slacky1965/electricity_meter_zrd/doc/images/board/board_3d_box_common.jpg

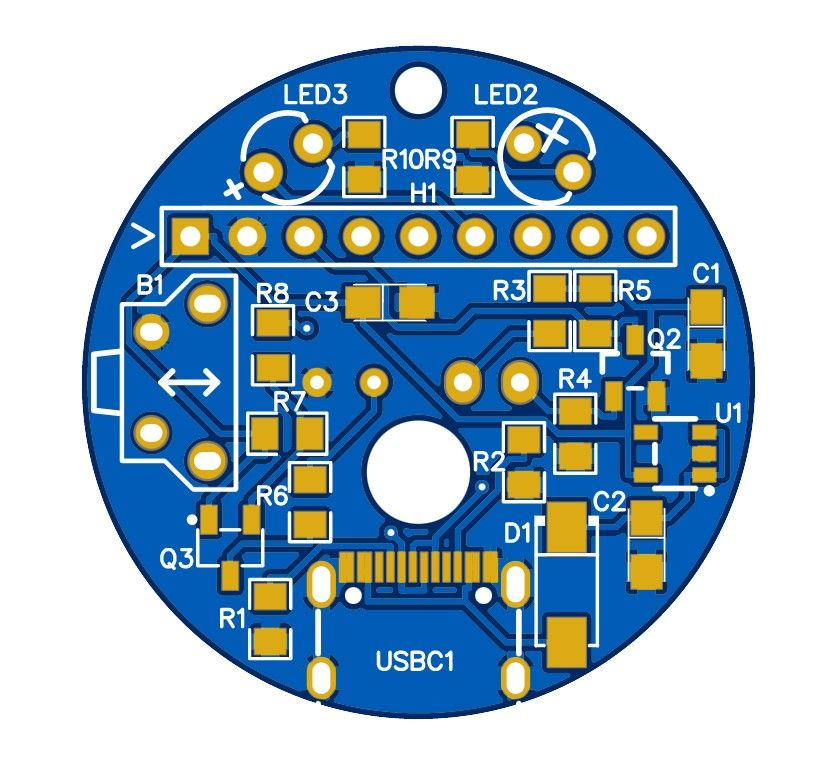
doc/images/board/board_3d_box_common.jpg
