slacky1965/electricity_meter_zrd/doc/images/board/board_ebyte_bottom.png

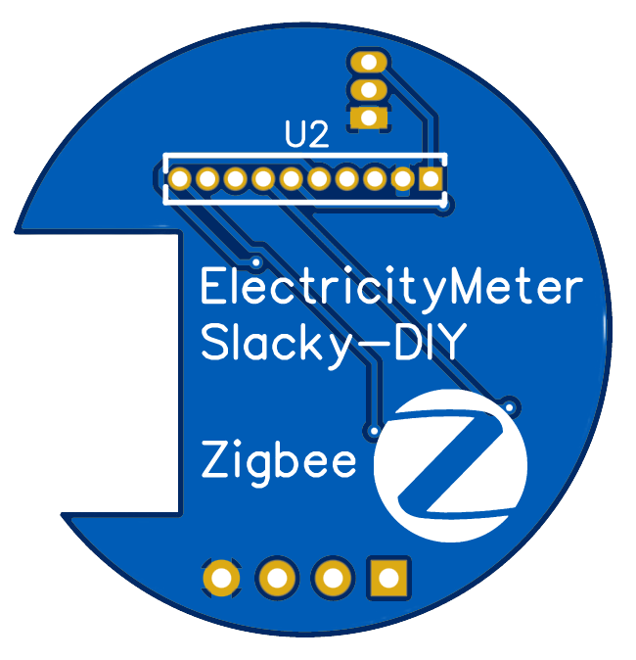
doc/images/board/board_ebyte_bottom.png
