slacky1965/electricity_meter_zrd/doc/images/box/box_common_e180.jpg

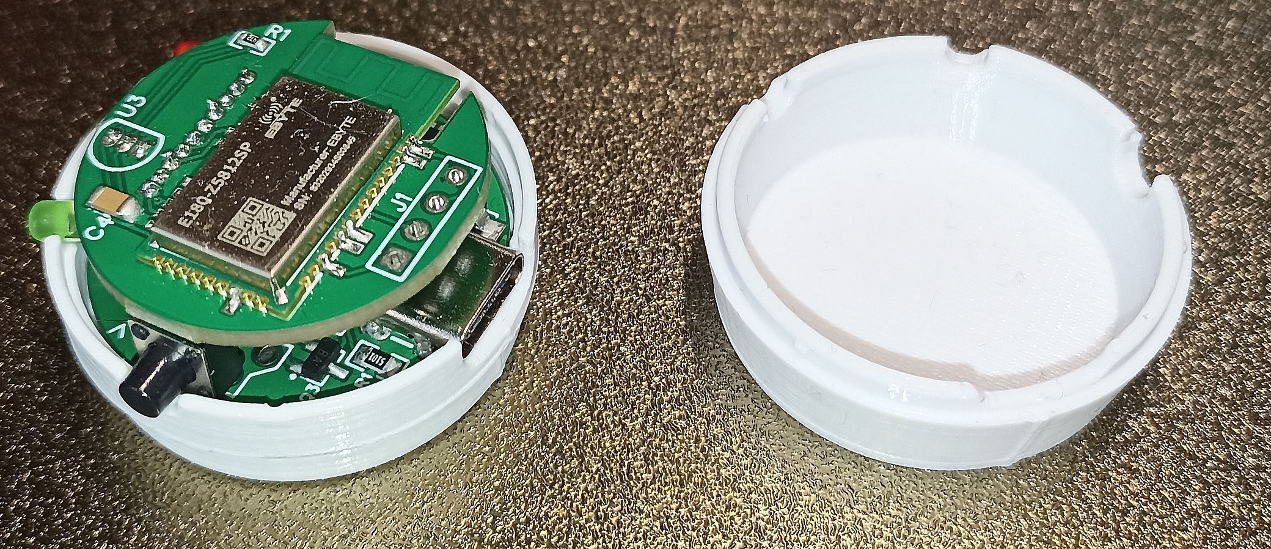
doc/images/box/box_common_e180.jpg
