slacky1965/electricity_meter_zrd/doc/images/box_drawing.jpg

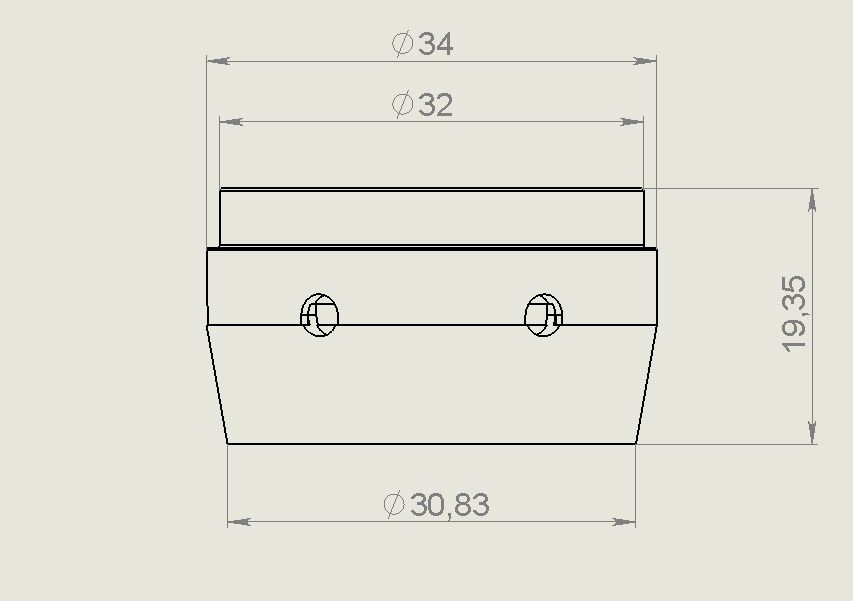
doc/images/box_drawing.jpg
