slacky1965/electricity_meter_zrd/doc/images/device_3d_box1.jpg

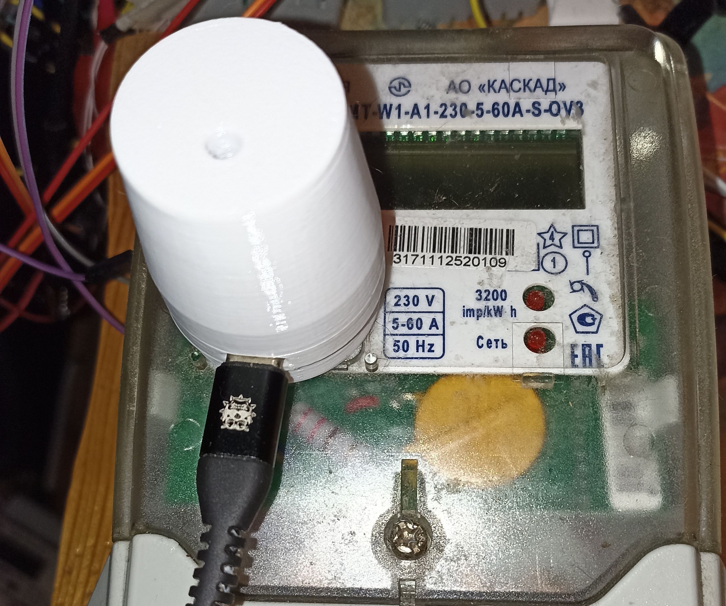
doc/images/device_3d_box1.jpg
