slacky1965/electricity_meter_zrd/doc/images/device_ztu_2.jpg

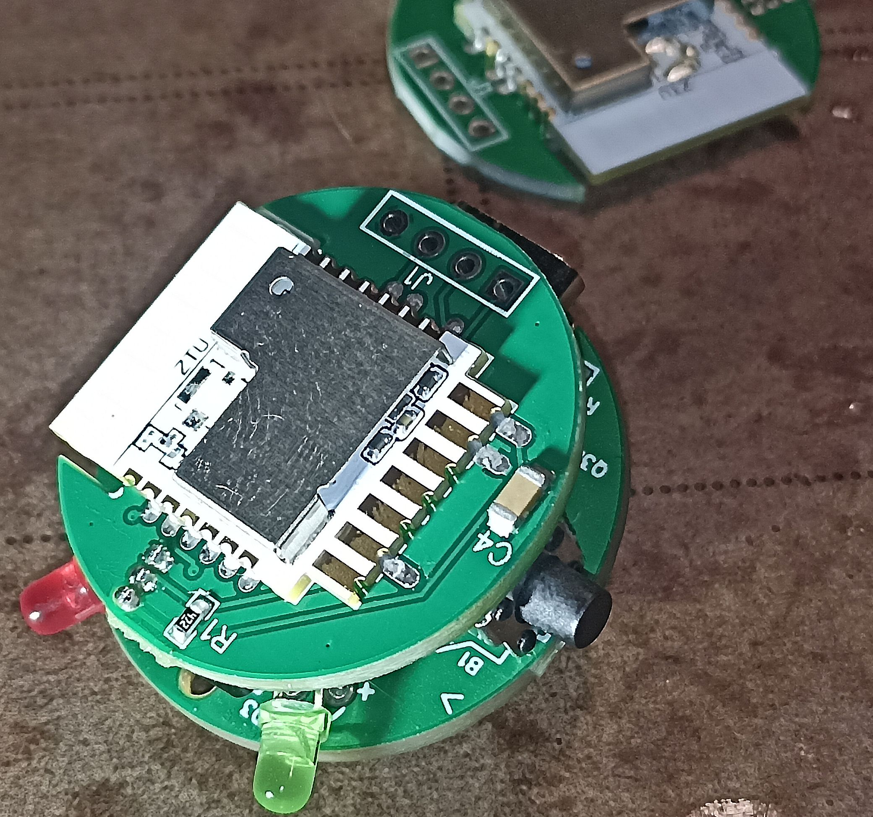
doc/images/device_ztu_2.jpg
