slacky1965/electricity_meter_zrd/doc/images/eclipse/eclipse5.jpg

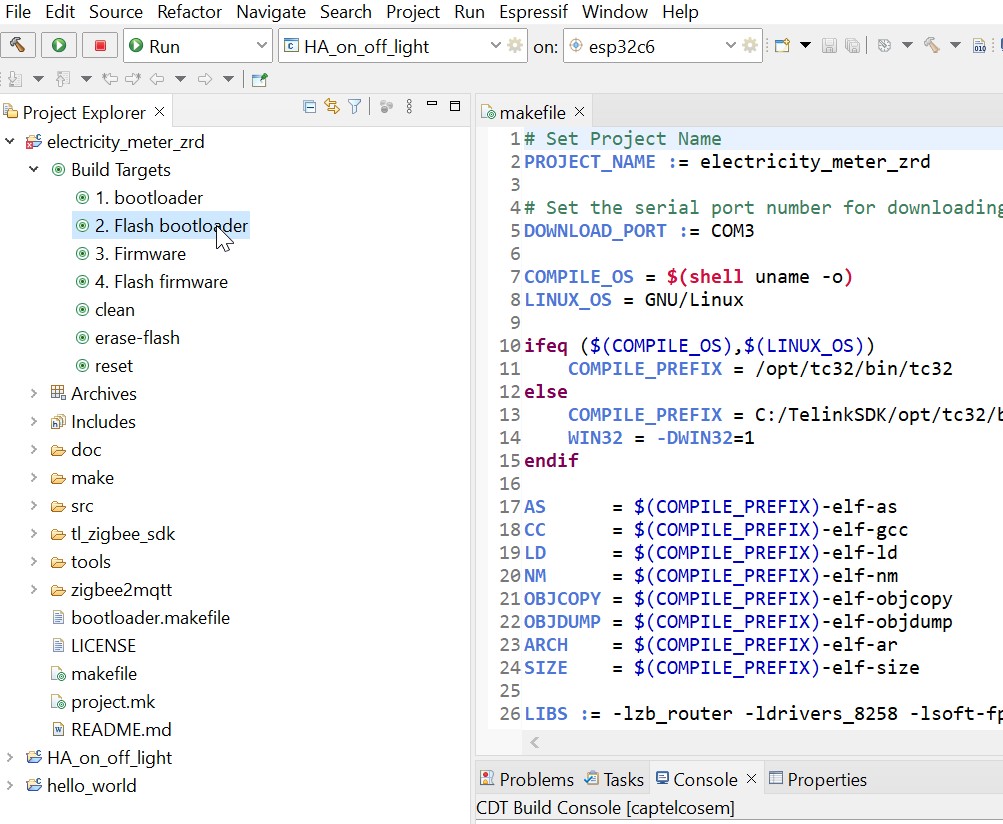
doc/images/eclipse/eclipse5.jpg
