slacky1965/electricity_meter_zrd/src/app_endpoint_cfg.c

#include "app_main.h"

#ifndef ZCL_BASIC_MFG_NAME
#define ZCL_BASIC_MFG_NAME     		{6,'T','E','L','I','N','K'}
#endif
#ifndef ZCL_BASIC_MODEL_ID
#define ZCL_BASIC_MODEL_ID	   		{8,'T','L','S','R','8','2','x','x'}
#endif
#ifndef ZCL_BASIC_SW_BUILD_ID
#define ZCL_BASIC_SW_BUILD_ID     	{10,'0','1','2','2','0','5','2','0','1','7'}
#endif

#define R               ACCESS_CONTROL_READ
#define RW              ACCESS_CONTROL_READ | ACCESS_CONTROL_WRITE
#define RR              ACCESS_CONTROL_READ | ACCESS_CONTROL_REPORTABLE

#define ZCL_UINT8       ZCL_DATA_TYPE_UINT8
#define ZCL_UINT16      ZCL_DATA_TYPE_UINT16
#define ZCL_UINT24      ZCL_DATA_TYPE_UINT24
#define ZCL_UINT32      ZCL_DATA_TYPE_UINT32
#define ZCL_UINT48      ZCL_DATA_TYPE_UINT48
#define ZCL_INT16       ZCL_DATA_TYPE_INT16
#define ZCL_ENUM8       ZCL_DATA_TYPE_ENUM8
#define ZCL_ENUM16      ZCL_DATA_TYPE_ENUM16
#define ZCL_BITMAP8     ZCL_DATA_TYPE_BITMAP8
#define ZCL_BITMAP16    ZCL_DATA_TYPE_BITMAP16
#define ZCL_BITMAP32    ZCL_DATA_TYPE_BITMAP32
#define ZCL_BOOLEAN     ZCL_DATA_TYPE_BOOLEAN
#define ZCL_CHAR_STR    ZCL_DATA_TYPE_CHAR_STR
#define ZCL_OCTET_STR   ZCL_DATA_TYPE_OCTET_STR
#define ZCL_UTC         ZCL_DATA_TYPE_UTC
#define ZCL_IEEE_ADDR   ZCL_DATA_TYPE_IEEE_ADDR

/**
 *  @brief Definition for Incoming cluster / Sever Cluster
 */
const uint16_t app_inClusterList[] = {
    ZCL_CLUSTER_GEN_BASIC,
    ZCL_CLUSTER_GEN_IDENTIFY,
#ifdef ZCL_ZLL_COMMISSIONING
    ZCL_CLUSTER_TOUCHLINK_COMMISSIONING,
#endif
#ifdef ZCL_POLL_CTRL
    ZCL_CLUSTER_GEN_POLL_CONTROL,
#endif
    ZCL_CLUSTER_SE_METERING,
    ZCL_CLUSTER_MS_ELECTRICAL_MEASUREMENT,
    ZCL_CLUSTER_GEN_DEVICE_TEMP_CONFIG,
};

/**
 *  @brief Definition for Outgoing cluster / Client Cluster
 */
const uint16_t app_outClusterList[] = {
    ZCL_CLUSTER_GEN_BASIC,
#ifdef ZCL_GROUP
    ZCL_CLUSTER_GEN_GROUPS,
#endif
#ifdef ZCL_SCENE
    ZCL_CLUSTER_GEN_SCENES,
#endif
#ifdef ZCL_ON_OFF
    ZCL_CLUSTER_GEN_ON_OFF,
#endif
#ifdef ZCL_LEVEL_CTRL
    ZCL_CLUSTER_GEN_LEVEL_CONTROL,
#endif
#ifdef ZCL_OTA
    ZCL_CLUSTER_OTA,
#endif
#ifdef ZCL_ZLL_COMMISSIONING
    ZCL_CLUSTER_TOUCHLINK_COMMISSIONING,
#endif
    ZCL_CLUSTER_GEN_TIME,
    ZCL_CLUSTER_SE_METERING,
};

/**
 *  @brief Definition for Server cluster number and Client cluster number
 */
#define APP_IN_CLUSTER_NUM      (sizeof(app_inClusterList)/sizeof(app_inClusterList[0]))
#define APP_OUT_CLUSTER_NUM     (sizeof(app_outClusterList)/sizeof(app_outClusterList[0]))

/**
 *  @brief Definition for simple description for HA profile
 */
const af_simple_descriptor_t app_simpleDesc =
{
    HA_PROFILE_ID,                          /* Application profile identifier */
    HA_DEV_METER_INTERFACE,                 /* Application device identifier */
    APP_ENDPOINT_1,                         /* Endpoint */
    1,                                      /* Application device version */
    0,                                      /* Reserved */
    APP_IN_CLUSTER_NUM,                     /* Application input cluster count */
    APP_OUT_CLUSTER_NUM,                    /* Application output cluster count */
    (uint16_t *)app_inClusterList,          /* Application input cluster list */
    (uint16_t *)app_outClusterList,         /* Application output cluster list */
};

/* Basic */
zcl_basicAttr_t g_zcl_basicAttrs =
{
    .zclVersion     = 0x03,
    .appVersion     = APP_RELEASE,
    .stackVersion   = (STACK_RELEASE|STACK_BUILD),
    .hwVersion      = HW_VERSION,
    .manuName       = ZCL_BASIC_MFG_NAME,
    .modelId        = ZCL_BASIC_MODEL_ID,
    .dateCode       = ZCL_BASIC_DATE_CODE,
    .powerSource    = POWER_SOURCE_MAINS_1_PHASE,
    .swBuildId      = ZCL_BASIC_SW_BUILD_ID,
    .deviceEnable   = TRUE,
};

uint8_t zclVersionServer;

const zclAttrInfo_t basic_attrTbl[] =
{
    { ZCL_ATTRID_BASIC_ZCL_VER,             ZCL_UINT8,      R,  (uint8_t*)&g_zcl_basicAttrs.zclVersion      },
    { ZCL_ATTRID_BASIC_APP_VER,             ZCL_UINT8,      R,  (uint8_t*)&g_zcl_basicAttrs.appVersion      },
    { ZCL_ATTRID_BASIC_STACK_VER,           ZCL_UINT8,      R,  (uint8_t*)&g_zcl_basicAttrs.stackVersion    },
    { ZCL_ATTRID_BASIC_HW_VER,              ZCL_UINT8,      R,  (uint8_t*)&g_zcl_basicAttrs.hwVersion       },
    { ZCL_ATTRID_BASIC_MFR_NAME,            ZCL_CHAR_STR,   R,  (uint8_t*)g_zcl_basicAttrs.manuName         },
    { ZCL_ATTRID_BASIC_MODEL_ID,            ZCL_CHAR_STR,   R,  (uint8_t*)g_zcl_basicAttrs.modelId          },
    { ZCL_ATTRID_BASIC_DATE_CODE,           ZCL_CHAR_STR,   R,  (uint8_t*)g_zcl_basicAttrs.dateCode         },
    { ZCL_ATTRID_BASIC_POWER_SOURCE,        ZCL_ENUM8,      R,  (uint8_t*)&g_zcl_basicAttrs.powerSource     },
    { ZCL_ATTRID_BASIC_DEV_ENABLED,         ZCL_BOOLEAN,    RW, (uint8_t*)&g_zcl_basicAttrs.deviceEnable    },
    { ZCL_ATTRID_BASIC_SW_BUILD_ID,         ZCL_CHAR_STR,   R,  (uint8_t*)&g_zcl_basicAttrs.swBuildId       },

    { ZCL_ATTRID_GLOBAL_CLUSTER_REVISION,   ZCL_UINT16,     R,  (uint8_t*)&zcl_attr_global_clusterRevision  },
};

#define ZCL_BASIC_ATTR_NUM    sizeof(basic_attrTbl) / sizeof(zclAttrInfo_t)

uint8_t zclVersionServer;

const zclAttrInfo_t version_attrTbl[] =
{
    { ZCL_ATTRID_BASIC_ZCL_VER,             ZCL_UINT8,      R,  (uint8_t*)&zclVersionServer                 },

    { ZCL_ATTRID_GLOBAL_CLUSTER_REVISION,   ZCL_UINT16,     R,  (uint8_t*)&zcl_attr_global_clusterRevision  },
};

#define ZCL_BASIC_SERVER_ATTR_NUM    sizeof(version_attrTbl) / sizeof(zclAttrInfo_t)


/* Identify */
zcl_identifyAttr_t g_zcl_identifyAttrs =
{
    .identifyTime   = 0x0000,
};

const zclAttrInfo_t identify_attrTbl[] =
{
    { ZCL_ATTRID_IDENTIFY_TIME,             ZCL_UINT16,     RW, (uint8_t*)&g_zcl_identifyAttrs.identifyTime },

    { ZCL_ATTRID_GLOBAL_CLUSTER_REVISION,   ZCL_UINT16,     R,  (uint8_t*)&zcl_attr_global_clusterRevision  },
};

#define ZCL_IDENTIFY_ATTR_NUM    sizeof(identify_attrTbl) / sizeof(zclAttrInfo_t)

zcl_timeAttr_t g_zcl_timeAttrs = {
    .time_utc = 0xffffffff,
};

const zclAttrInfo_t time_attrTbl[] =
{
    { ZCL_ATTRID_TIME,                      ZCL_UTC,    RW, (uint8_t*)&g_zcl_timeAttrs.time_utc         },

    { ZCL_ATTRID_GLOBAL_CLUSTER_REVISION,   ZCL_UINT16, R,  (uint8_t*)&zcl_attr_global_clusterRevision  },
};

#define ZCL_TIME_ATTR_NUM    sizeof(time_attrTbl) / sizeof(zclAttrInfo_t)

zcl_seAttr_t g_zcl_seAttrs = {
    .tariff_1 = 0,
    .tariff_2 = 0,
    .tariff_3 = 0,
    .tariff_4 = 0,
    .unit_of_measure = 0x00,                                        // kWh
    .multiplier = 1,
    .divisor = 1,
    .summation_formatting = 0xFA,                                   // bit7 - 1, bit6-bit3 - 15, bit2-bit0 - 2 (b11111010)
    .status = 0,
    .device_type = 0,                                               // 0 - Electric Metering
    .battery_percentage = 100,
    .serial_number = {8,'1','1','1','1','1','1','1','1'},
    .date_release = {10,'x','x','.','x','x','.','x','x','x','x'},
    .device_model = DEVICE_UNDEFINED, // Electric Metering
    .device_address = 0,
    .device_name = {9,'N','o',' ','D','e','v','i','c','e'},
    .device_password = {1, '0'},
    .measurement_period = DEFAULT_MEASUREMENT_PERIOD,
};

const zclAttrInfo_t se_attrTbl[] = {
    {ZCL_ATTRID_CURRENT_SUMMATION_DELIVERD,         ZCL_UINT48,     RR, (uint8_t*)&g_zcl_seAttrs.cur_sum_delivered      },
    {ZCL_ATTRID_CURRENT_TIER_1_SUMMATION_DELIVERD,  ZCL_UINT48,     RR, (uint8_t*)&g_zcl_seAttrs.tariff_1               },
    {ZCL_ATTRID_CURRENT_TIER_2_SUMMATION_DELIVERD,  ZCL_UINT48,     RR, (uint8_t*)&g_zcl_seAttrs.tariff_2               },
    {ZCL_ATTRID_CURRENT_TIER_3_SUMMATION_DELIVERD,  ZCL_UINT48,     RR, (uint8_t*)&g_zcl_seAttrs.tariff_3               },
    {ZCL_ATTRID_CURRENT_TIER_4_SUMMATION_DELIVERD,  ZCL_UINT48,     RR, (uint8_t*)&g_zcl_seAttrs.tariff_4               },
    {ZCL_ATTRID_STATUS,                             ZCL_BITMAP8,    RR,  (uint8_t*)&g_zcl_seAttrs.status                },
    {ZCL_ATTRID_UNIT_OF_MEASURE,                    ZCL_UINT8,      R,  (uint8_t*)&g_zcl_seAttrs.unit_of_measure        },
    {ZCL_ATTRID_MULTIPLIER,                         ZCL_UINT24,     RR, (uint8_t*)&g_zcl_seAttrs.multiplier             },
    {ZCL_ATTRID_DIVISOR,                            ZCL_UINT24,     RR, (uint8_t*)&g_zcl_seAttrs.divisor                },
    {ZCL_ATTRID_SUMMATION_FORMATTING,               ZCL_BITMAP8,    R,  (uint8_t*)&g_zcl_seAttrs.summation_formatting   },
    {ZCL_ATTRID_REMAINING_BATTERY_LIFE,             ZCL_UINT8,      RR, (uint8_t*)&g_zcl_seAttrs.battery_percentage     },
    {ZCL_ATTRID_METER_SERIAL_NUMBER,                ZCL_OCTET_STR,  RR, (uint8_t*)&g_zcl_seAttrs.serial_number          },
    {ZCL_ATTRID_METERING_DEVICE_TYPE,               ZCL_BITMAP8,    R,  (uint8_t*)&g_zcl_seAttrs.device_type            },
    {ZCL_ATTRID_CUSTOM_DEVICE_MANUFACTURER,         ZCL_ENUM8,      RW, (uint8_t*)&g_zcl_seAttrs.device_model           },
    {ZCL_ATTRID_CUSTOM_DEVICE_ADDRESS,              ZCL_UINT32,     RW, (uint8_t*)&g_zcl_seAttrs.device_address         },
    {ZCL_ATTRID_CUSTOM_DEVICE_PASSWORD,             ZCL_OCTET_STR,  RW, (uint8_t*)&g_zcl_seAttrs.device_password        },
    {ZCL_ATTRID_CUSTOM_MEASUREMENT_PERIOD,          ZCL_UINT8,      RW, (uint8_t*)&g_zcl_seAttrs.measurement_period     },
    {ZCL_ATTRID_CUSTOM_DATE_RELEASE,                ZCL_OCTET_STR,  RR, (uint8_t*)&g_zcl_seAttrs.date_release           },
    {ZCL_ATTRID_CUSTOM_DEVICE_MODEL,                ZCL_OCTET_STR,  RR, (uint8_t*)&g_zcl_seAttrs.device_name            },

    { ZCL_ATTRID_GLOBAL_CLUSTER_REVISION,           ZCL_UINT16,     R,  (uint8_t*)&zcl_attr_global_clusterRevision      },
};

#define ZCL_SE_ATTR_NUM    sizeof(se_attrTbl) / sizeof(zclAttrInfo_t)

zcl_msAttr_t g_zcl_msAttrs = {
    .type = 0x09,               // bit0: Active measurement (AC). bit3: Phase A measurement
    .current = 0xffff,
    .current_multiplier = 1,
    .current_divisor = 1,
    .voltage = 0xffff,
    .voltage_multiplier = 1,
    .voltage_divisor = 1,
    .power = 0xffff,
    .power_multiplier = 1,
    .power_divisor = 1,
};

const zclAttrInfo_t ms_attrTbl[] = {
    {ZCL_ATTRID_MEASUREMENT_TYPE,           ZCL_BITMAP32, R,    (uint8_t*)&g_zcl_msAttrs.type               },
    {ZCL_ATTRID_LINE_CURRENT,               ZCL_UINT16,   RR,   (uint8_t*)&g_zcl_msAttrs.current            },
    {ZCL_ATTRID_AC_CURRENT_MULTIPLIER,      ZCL_UINT16,   RR,   (uint8_t*)&g_zcl_msAttrs.current_multiplier },
    {ZCL_ATTRID_AC_CURRENT_DIVISOR,         ZCL_UINT16,   RR,   (uint8_t*)&g_zcl_msAttrs.current_divisor    },
    {ZCL_ATTRID_RMS_VOLTAGE,                ZCL_UINT16,   RR,   (uint8_t*)&g_zcl_msAttrs.voltage            },
    {ZCL_ATTRID_AC_VOLTAGE_MULTIPLIER,      ZCL_UINT16,   RR,   (uint8_t*)&g_zcl_msAttrs.voltage_multiplier },
    {ZCL_ATTRID_AC_VOLTAGE_DIVISOR,         ZCL_UINT16,   RR,   (uint8_t*)&g_zcl_msAttrs.voltage_divisor    },
    {ZCL_ATTRID_APPARENT_POWER,             ZCL_UINT16,   RR,   (uint8_t*)&g_zcl_msAttrs.power              },
    {ZCL_ATTRID_AC_POWER_MULTIPLIER,        ZCL_UINT16,   RR,   (uint8_t*)&g_zcl_msAttrs.power_multiplier   },
    {ZCL_ATTRID_AC_POWER_DIVISOR,           ZCL_UINT16,   RR,   (uint8_t*)&g_zcl_msAttrs.power_divisor      },

    { ZCL_ATTRID_GLOBAL_CLUSTER_REVISION,   ZCL_UINT16,   R,    (uint8_t*)&zcl_attr_global_clusterRevision  },
};

#define ZCL_MS_ATTR_NUM    sizeof(ms_attrTbl) / sizeof(zclAttrInfo_t)

zcl_tempAttr_t g_zcl_tempAttrs = {
        .temperature    = 22,
        .alarm_mask     = 0x02, /* bit0 = 0 (low alarm is disabled), bit1 = 1 (high alarm is enabled) */
        .high_threshold = 70,   /* 70 in degrees Celsius                                              */
};

const zclAttrInfo_t temp_attrTbl[] =
{
    {ZCL_ATTRID_DEV_TEMP_CURR_TEMP,         ZCL_INT16,      RR, (uint8_t*)&g_zcl_tempAttrs.temperature      },
    {ZCL_ATTRID_DEV_TEMP_ALARM_MASK,        ZCL_BITMAP8,    RW, (uint8_t*)&g_zcl_tempAttrs.alarm_mask       },
    {ZCL_ATTRID_DEV_TEMP_HIGH_THRES,        ZCL_INT16,      RW, (uint8_t*)&g_zcl_tempAttrs.high_threshold   },

    { ZCL_ATTRID_GLOBAL_CLUSTER_REVISION,   ZCL_UINT16,     R,  (uint8_t*)&zcl_attr_global_clusterRevision  },
};

#define ZCL_TEMP_ATTR_NUM    sizeof(temp_attrTbl) / sizeof(zclAttrInfo_t)

#ifdef ZCL_GROUP
/* Group */
zcl_groupAttr_t g_zcl_groupAttrs =
{
    .nameSupport    = 0,
};

const zclAttrInfo_t group_attrTbl[] =
{
    { ZCL_ATTRID_GROUP_NAME_SUPPORT,        ZCL_BITMAP8,    R,  (uint8_t*)&g_zcl_groupAttrs.nameSupport     },

    { ZCL_ATTRID_GLOBAL_CLUSTER_REVISION,   ZCL_UINT16,     R,  (uint8_t*)&zcl_attr_global_clusterRevision  },
};

#define ZCL_GROUP_ATTR_NUM    sizeof(group_attrTbl) / sizeof(zclAttrInfo_t)
#endif

#ifdef ZCL_SCENE
/* Scene */
zcl_sceneAttr_t g_zcl_sceneAttrs =
{
    .sceneCount     = 0,
    .currentScene   = 0,
    .currentGroup   = 0x0000,
    .sceneValid     = FALSE,
    .nameSupport    = 0,
};

const zclAttrInfo_t scene_attrTbl[] =
{
    { ZCL_ATTRID_SCENE_SCENE_COUNT,         ZCL_UINT8,    R,  (uint8_t*)&g_zcl_sceneAttrs.sceneCount     },
    { ZCL_ATTRID_SCENE_CURRENT_SCENE,       ZCL_UINT8,    R,  (uint8_t*)&g_zcl_sceneAttrs.currentScene   },
    { ZCL_ATTRID_SCENE_CURRENT_GROUP,       ZCL_UINT16,   R,  (uint8_t*)&g_zcl_sceneAttrs.currentGroup   },
    { ZCL_ATTRID_SCENE_SCENE_VALID,         ZCL_BOOLEAN,  R,  (uint8_t*)&g_zcl_sceneAttrs.sceneValid     },
    { ZCL_ATTRID_SCENE_NAME_SUPPORT,        ZCL_BITMAP8,  R,  (uint8_t*)&g_zcl_sceneAttrs.nameSupport    },

    { ZCL_ATTRID_GLOBAL_CLUSTER_REVISION,   ZCL_UINT16,   R,  (uint8_t*)&zcl_attr_global_clusterRevision},
};

#define ZCL_SCENE_ATTR_NUM   sizeof(scene_attrTbl) / sizeof(zclAttrInfo_t)
#endif



/**
 *  @brief Definition for simple light ZCL specific cluster
 */
const zcl_specClusterInfo_t g_appClusterList[] =
{
    {ZCL_CLUSTER_GEN_BASIC,                 MANUFACTURER_CODE_NONE, ZCL_BASIC_ATTR_NUM,     basic_attrTbl,      zcl_basic_register,             app_basicCb     },
    {ZCL_CLUSTER_GEN_IDENTIFY,              MANUFACTURER_CODE_NONE, ZCL_IDENTIFY_ATTR_NUM,  identify_attrTbl,   zcl_identify_register,          app_identifyCb  },
#ifdef ZCL_GROUP
    {ZCL_CLUSTER_GEN_GROUPS,                MANUFACTURER_CODE_NONE, ZCL_GROUP_ATTR_NUM,     group_attrTbl,      zcl_group_register,             NULL            },
#endif
#ifdef ZCL_SCENE
    {ZCL_CLUSTER_GEN_SCENES,                MANUFACTURER_CODE_NONE, ZCL_SCENE_ATTR_NUM,     scene_attrTbl,      zcl_scene_register,             app_sceneCb     },
#endif
    {ZCL_CLUSTER_GEN_TIME,                  MANUFACTURER_CODE_NONE, ZCL_TIME_ATTR_NUM,      time_attrTbl,       zcl_time_register,              app_timeCb      },
    {ZCL_CLUSTER_SE_METERING,               MANUFACTURER_CODE_NONE, ZCL_SE_ATTR_NUM,        se_attrTbl,         zcl_metering_register,          app_meteringCb  },
    {ZCL_CLUSTER_MS_ELECTRICAL_MEASUREMENT, MANUFACTURER_CODE_NONE, ZCL_MS_ATTR_NUM,        ms_attrTbl,         zcl_electricalMeasure_register, NULL            },
    {ZCL_CLUSTER_GEN_DEVICE_TEMP_CONFIG,    MANUFACTURER_CODE_NONE, ZCL_TEMP_ATTR_NUM,      temp_attrTbl,       zcl_devTemperatureCfg_register, NULL            },
};

uint8_t APP_CB_CLUSTER_NUM = (sizeof(g_appClusterList)/sizeof(g_appClusterList[0]));
