slacky1965/electricity_meter_zrd/src/include/app_reporting.h

#ifndef SRC_INCLUDE_APP_REPORTING_H_
#define SRC_INCLUDE_APP_REPORTING_H_

typedef struct {
    ev_timer_event_t *timerReportMinEvt;
    ev_timer_event_t *timerReportMaxEvt;
    reportCfgInfo_t  *pEntry;
    uint32_t          time_posted;
} app_reporting_t;

typedef enum {
    DEVICE_MODEL = 0,
    CURR_TEMP,
    SERIAL_NUMBER,
    DATE_RELEASE,
    MULTIPLIER,
    DIVISOR,
    CUR_SUMM_DELIVERD,
    CUR_T1_SUMM_DELIVERD,
    CUR_T2_SUMM_DELIVERD,
    CUR_T3_SUMM_DELIVERD,
    CUR_T4_SUMM_DELIVERD,
    VOLTAGE_MULTIPLIER,
    VOLTAGE_DIVISOR,
    VOLTAGE,
    POWER_MULTIPLIER,
    POWER_DIVISOR,
    POWER,
    CURRENT_MULTIPLIER,
    CURRENT_DIVISOR,
    CURRENT,
    BATTERY_LIFE,
    ATTR_MAX
} attr_name_t;

extern app_reporting_t app_reporting[ZCL_REPORTING_TABLE_NUM];

void app_forcedReport(uint8_t endpoint, uint16_t claster_id, uint16_t attr_id);
void app_all_forceReporting();
void app_reporting_init();
void app_report_handler(void);

#endif /* SRC_INCLUDE_APP_REPORTING_H_ */
