slacky1965/electricity_meter_zrd/src/include/app_led.h

#ifndef SRC_INCLUDE_APP_LED_H_
#define SRC_INCLUDE_APP_LED_H_

#define LED_ON                      1
#define LED_OFF                     0

void led_init(void);
void led_on(uint32_t pin);
void led_off(uint32_t pin);

void light_blink_start(uint8_t times, uint16_t ledOnTime, uint16_t ledOffTime);
void light_blink_stop(void);

void light_init(void);
void light_on(void);
void light_off(void);
int32_t flashLedStatusCb(void *arg);


#endif /* SRC_INCLUDE_APP_LED_H_ */
